kermitsgonnakermicide/Lattice/Assets/keyboard with macropad.png

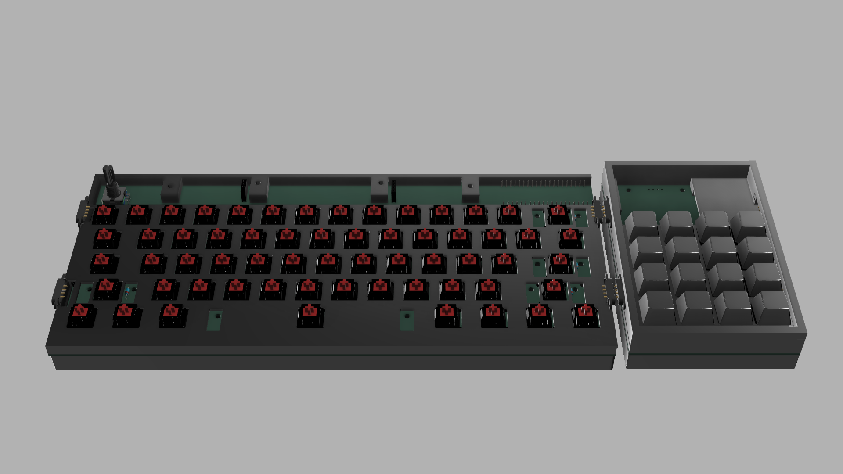
Assets/keyboard with macropad.png
